ut-ras/Demobots-Polargraph/PolargraphESP32/src/iot/iot_config.h

#ifndef IOT_CONFIG_H
#define IOT_CONFIG_H

#include <Arduino.h>

//WiFi Settings
//STA = connect to a WiFi network with name ssid
//AP = create a WiFi access point with name ssid
//AUTO = STA if it finds the network, AP if it does not
#define WIFI_MODE "AP"
const char * ssid = "Demobot";
const char * pass = "demobot1234";

//const char * hostname = "demobot_polargraph";

IPAddress ip;

#define STA_TIMEOUT_MS 3000       //for AUTO mode. when initializing WiFi, how long to look for existing AP before deploying one
#define MIN_UPDATE_MS 50          //for the webserver main thread, smallest update interval

#endif
